coseyfannitutti/mysterium/case/winkeyless/mysterium-open-layer.dxf

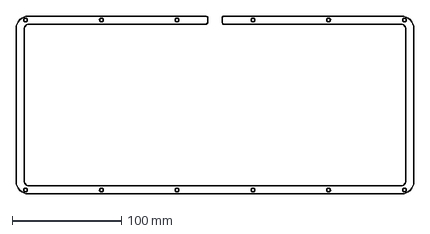
[picture p22: CAD file, 2020-04-24]
case/winkeyless/mysterium-open-layer.dxf
363.7 x 162.6 mm
