coseyfannitutti/mysterium/case/standard/mysterium-top-2.dxf

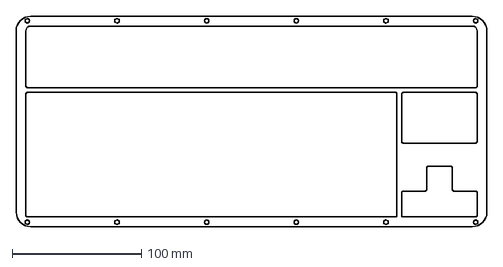
[picture p23: CAD file, 2020-04-24]
case/standard/mysterium-top-2.dxf
363.7 x 162.6 mm
